MikolajSzawerda/infrared-guided-rocket/thermo_guide/src/Camera/Camera.h

//
// Created by mszawerd on 24.05.23.
//

#ifndef CLIENTSERVER_CAMERA_H
#define CLIENTSERVER_CAMERA_H

#include "stdint.h"
#include "i2c.h"
#include <unistd.h>
#include <stdio.h>
#include <stdlib.h>
#include <string.h>
#include <math.h>

#define BUFFER_SIZE 64

#define MIN(X, Y) (((X) < (Y)) ? (X) : (Y))


/*=========================================================================
    I2C ADDRESS/BITS
    -----------------------------------------------------------------------*/
#define AMG88xx_ADDRESS (0x69)
/*=========================================================================*/

/*=========================================================================
    REGISTERS
    -----------------------------------------------------------------------*/
enum {
    AMG88xx_PCTL = 0x00,
    AMG88xx_RST = 0x01,
    AMG88xx_FPSC = 0x02,
    AMG88xx_INTC = 0x03,
    AMG88xx_STAT = 0x04,
    AMG88xx_SCLR = 0x05,
    // 0x06 reserved
    AMG88xx_AVE = 0x07,
    AMG88xx_INTHL = 0x08,
    AMG88xx_INTHH = 0x09,
    AMG88xx_INTLL = 0x0A,
    AMG88xx_INTLH = 0x0B,
    AMG88xx_IHYSL = 0x0C,
    AMG88xx_IHYSH = 0x0D,
    AMG88xx_TTHL = 0x0E,
    AMG88xx_TTHH = 0x0F,
    AMG88xx_INT_OFFSET = 0x010,
    AMG88xx_PIXEL_OFFSET = 0x80
};

enum power_modes {
    AMG88xx_NORMAL_MODE = 0x00,
    AMG88xx_SLEEP_MODE = 0x01,
    AMG88xx_STAND_BY_60 = 0x20,
    AMG88xx_STAND_BY_10 = 0x21
};

enum sw_resets {
    AMG88xx_FLAG_RESET = 0x30, AMG88xx_INITIAL_RESET = 0x3F
};

enum frame_rates {
    AMG88xx_FPS_10 = 0x00, AMG88xx_FPS_1 = 0x01
};

enum int_enables {
    AMG88xx_INT_DISABLED = 0x00, AMG88xx_INT_ENABLED = 0x01
};

enum int_modes {
    AMG88xx_DIFFERENCE = 0x00, AMG88xx_ABSOLUTE_VALUE = 0x01
};

/*=========================================================================*/

#define AMG88xx_PIXEL_ARRAY_SIZE 64
#define AMG88xx_PIXEL_TEMP_CONVERSION .25
#define AMG88xx_THERMISTOR_CONVERSION .0625

i2c_t* begin();

void readPixelsRaw(i2c_t* i2c_dev, uint8_t *buf, uint8_t pixels);

void readPixels(i2c_t* i2c_dev, float *buf, uint8_t pixels);

uint8_t read8(i2c_t* i2c_dev, uint8_t reg);

void write8(i2c_t* i2c_dev,uint8_t reg, uint8_t *buf);

void plain_read(i2c_t* i2c_dev, uint8_t reg, uint8_t *buf, uint8_t num);

float signedMag12ToFloat(uint16_t val);

float int12ToFloat(uint16_t val);

void generate_fake_circle(float* buffer, double time);

#endif //CLIENTSERVER_CAMERA_H
